immortal-sniper1/cross_band_handy_walkie_talkie/Hardware/PICS/IMG_79061.JPG

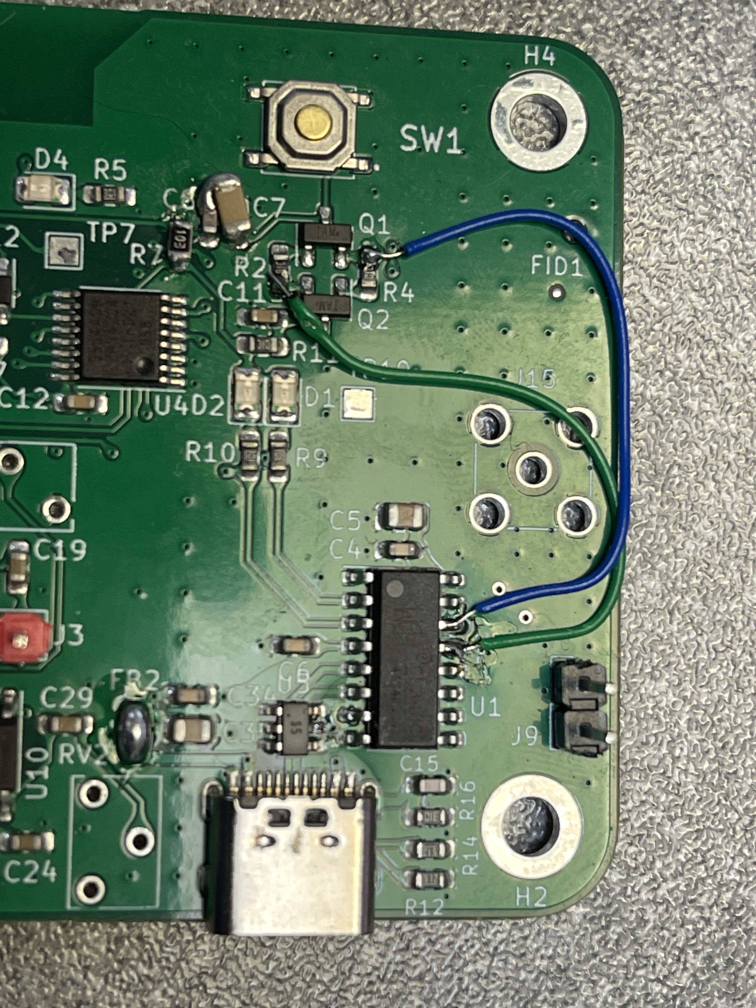
Hardware/PICS/IMG_79061.JPG
