immortal-sniper1/cross_band_handy_walkie_talkie/Hardware/cross_band_handy_walkie_talkie_ES8388/Power_circuit_SIM/POWER.asc

C1: cap; 220µ
C2: cap; 10µ
C3: cap; 10µ
C4: cap; 1p
M1: nmos; 2N7002
R1: res; 5
R2: res; 10k
R3: res; 10k
R4: res; 10k
U1: ADM7171-3.3
U2: AO3401A
U3: AO3401A
U4: AO3401A
V1: voltage; PWL(0 0 25m 0 25.001m 5 50m 5 50.001m 0 75m 0)
V2: voltage; 3.6
Named nets: 0, usb, batt, LOAD, RAW_3V3
.tran 0 100m 0 100n startup
.model My_PMOS PMOS(VTO=-2.5 CGS=645p)
.model My_NMOS NMOS(VTO=1.6 CGS=50p)
