immortal-sniper1/cross_band_handy_walkie_talkie/examples/test-wifi/test-wifi.ino

#include <WiFi.h>

const char* ssid = "Your SID";
const char* password = "Your Password";

void setup() {
  Serial.begin(115200);
  while (!Serial);

  WiFi.mode(WIFI_STA);
  WiFi.begin(ssid, password);
  Serial.print("Connecting to WiFi ..");
  while (WiFi.status() != WL_CONNECTED) {
    Serial.print('.');
    delay(1000);
  }
}

void loop() {
  Serial.print(WiFi.localIP());
  Serial.print(" RRSI: ");
  Serial.println(WiFi.RSSI());
  delay(3000);

}
